thomas-maurice/SmartSensorWifi/Web/doge.jpeg

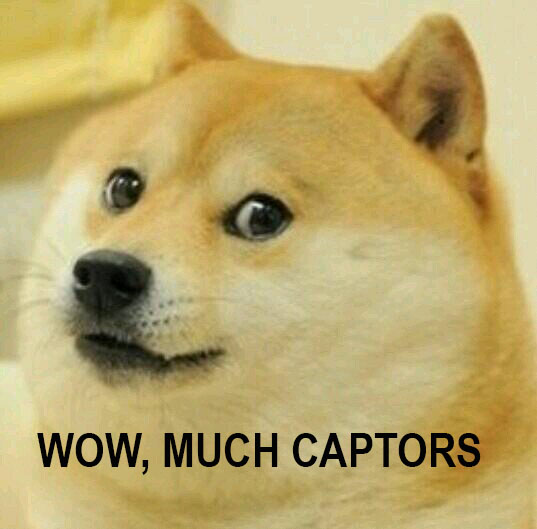
Web/doge.jpeg
