thomas-maurice/SmartSensorWifi/Arduino/src/ds1302.c

/*
 *
 *	Copyright (C) 2014 Thomas MAURICE <tmaurice59@gmail.com>
 *
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
 *	You should have received a copy of the GNU General Public License along
 *	with this program; if not, write to the Free Software Foundation, Inc.,
 *	51 Franklin Street, Fifth Floor, Boston, MA 02110-1301 USA.
 */

/**
 * \file ds1302.c
 * \author Thomas Maurice
 * 
 * \brief Implements an interface to the DS1302 RTC chip
 * \version 0.1
 * 
 */

#include <ds1302.h>

/**
 * Initializes the data transfert between the RTC and the chip.
 * This will configure the DDR as well as the initial state of
 * the lines.
 */
void ds1302_init_transfert() {
	// Set CE low and as an output
	sbi(DS1302_CE_DDR, DS1302_CE_PIN);
	cbi(DS1302_CE_PORT, DS1302_CE_PIN);
	
	// Set the clock low and as an output
	sbi(DS1302_CLK_DDR, DS1302_CLK_PIN);
	cbi(DS1302_CLK_PORT, DS1302_CLK_PIN);
	
	// Finally start the transfert setting the CE high
	sbi(DS1302_CE_PORT, DS1302_CE_PIN);
	
	_delay_us(4);
}

/**
 * Closes all the data transfers. This will disable the RTC CE line.
 */
void ds1302_end_transfert() {
	// Finally end the transfert setting the CE low
	cbi(DS1302_CE_PORT, DS1302_CE_PIN);
	
	_delay_us(4);
}

/**
 * Shifts a byte to the RTC
 * 
 * \param [in] byte The byte to shift
 */
void ds1302_shift_byte(uint8_t byte) {
	for(uint8_t i = 0; i < 8; i++) {
		cbi(DS1302_IO_PORT, DS1302_IO_PIN);
		DS1302_IO_PORT |= (((gbi(byte,i))<<DS1302_IO_PIN));
		_delay_us(1);
		sbi(DS1302_CLK_PORT, DS1302_CLK_PIN);
		_delay_us(1);
		cbi(DS1302_CLK_PORT, DS1302_CLK_PIN);
		_delay_us(1);
	}
}

/**
 * This function will write to a register of the RTC. This function
 * can be user either to configure the chip or to use the general
 * purpose ram.
 * 
 * \param [in] addr The address to write
 * \param [in] value The value to write
 * \param [in] target The target. Is either the clock register or the RAM register.
 * This value has either DS1302_CLOCK or DS1302_RAM value.
 */
void ds1302_write_register(uint8_t addr, uint8_t value, uint8_t target) {
	ds1302_init_transfert();
	uint8_t cmd = 0x0;
	cmd |= 0x80 | target | DS1302_WRITE_BYTE; // We want to write
	cmd |= ((addr&0x1F) << 1); // Let's put the address
	
	// Now we shift out the whole thing
	ds1302_shift_byte(cmd);
	ds1302_shift_byte(value);
	
	ds1302_end_transfert();
}

/**
 * Read the value stored in a register of the chip and returns it. This
 * function can be user either to read the chip or to use the general
 * purpose ram.
 * 
 * \param [in] addr The address to read
 * \param [in] target The target. Is either the clock register or the RAM register.
 * This value has either DS1302_CLOCK or DS1302_RAM value.
 * 
 * \return The value read
 */
uint8_t ds1302_read_register(uint8_t addr, uint8_t target) {
	ds1302_init_transfert();
	uint8_t cmd = 0x0;
	cmd |= 0x80 | target | DS1302_READ_BYTE; // We want to read from the clock
	cmd |= ((addr) << 1); // Let's put the address
	uint8_t res = 0x0;
	
	// Put the I/O line to output
	sbi(DS1302_IO_DDR, DS1302_IO_PIN);
	
	// Now we shift out the whole thing
	ds1302_shift_byte(cmd);
	
	// Put IO line to input & disable pull up
	cbi(DS1302_IO_DDR, DS1302_IO_PIN);
	cbi(DS1302_IO_PORT, DS1302_IO_PIN);
	
	for(uint8_t i = 0; i < 8; i++) {
		res |= (gbi(DS1302_IO_RD_PORT, DS1302_IO_PIN)<<i);
		
		_delay_us(1);
		sbi(DS1302_CLK_PORT, DS1302_CLK_PIN);
		_delay_us(1);
		cbi(DS1302_CLK_PORT, DS1302_CLK_PIN);
		_delay_us(1);
	}
	
	// Restore the I/O line to output
	sbi(DS1302_IO_DDR, DS1302_IO_PIN);
	cbi(DS1302_IO_PORT, DS1302_IO_PIN);
	
	ds1302_end_transfert();
	
	return res;
}

/**
 * Creates a timestring for the current date following the format :
 * DD/MM/YY HH:MM:SS so it is 18 chars long, including the null terminator.
 * 
 * \param [inout] time_string the pointer on the memory zone needed.
 */
void get_time_string(char* time_string) {
	uint8_t result = 0;
	result = ds1302_read_register(DS1302_SECONDS, DS1302_CLOCK);
	time_string[16] = (result & 0x0F) + '0';
	time_string[15] = ((result>>4) & 0x0F) + '0';
	time_string[14] = ':';
	result = ds1302_read_register(DS1302_MINUTES, DS1302_CLOCK);
	time_string[13] = (result & 0x0F) + '0';
	time_string[12] = ((result>>4) & 0x0F) + '0';
	time_string[11] = ':';
	result = ds1302_read_register(DS1302_HOURS, DS1302_CLOCK);
	time_string[10] = (result & 0x0F) + '0';
	time_string[9] = ((result>>4) & 0x0F) + '0';
	time_string[8] = ' ';
	result = ds1302_read_register(DS1302_YEAR, DS1302_CLOCK);
	time_string[7] = (result & 0x0F) + '0';
	time_string[6] = ((result>>4) & 0x0F) + '0';
	time_string[5] = '/';
	result = ds1302_read_register(DS1302_MONTH, DS1302_CLOCK);
	time_string[4] = (result & 0x0F) + '0';
	time_string[3] = ((result>>4) & 0x0F) + '0';
	time_string[2] = '/';
	result = ds1302_read_register(DS1302_DATE, DS1302_CLOCK);
	time_string[1] = (result & 0x0F) + '0';
	time_string[0] = ((result>>4) & 0x0F) + '0';
}

/**
 * Clears the CH bit. This will allow the clock to start.
 */
void ds1302_clear_clock_halt() {
	uint8_t r = ds1302_read_register(DS1302_SECONDS, DS1302_CLOCK);
	ds1302_write_register(DS1302_SECONDS, r & 0x7F, DS1302_CLOCK);
}

/**
 * Sets the time to the chip. The value are provided in natural binary,
 * the function will convert it to BCD.
 * 
 * \param [hrs] Hours
 * \param [mins] Minutes
 * \param [secs] Seconds
 */
void ds1302_set_time(uint8_t hrs, uint8_t mins, uint8_t secs) {
	ds1302_write_register(DS1302_SECONDS, dec_to_bcd(secs), DS1302_CLOCK);
	ds1302_write_register(DS1302_MINUTES, dec_to_bcd(mins), DS1302_CLOCK);
	ds1302_write_register(DS1302_HOURS, dec_to_bcd(hrs), DS1302_CLOCK);
}

/**
 * Sets the time to the chip. The value are provided in natural binary,
 * the function will convert it to BCD.
 * 
 * \param [day] Day
 * \param [month] Month
 * \param [year] Year
 */
void ds1302_set_date(uint8_t day, uint8_t month, uint16_t year) {
	ds1302_write_register(DS1302_DATE, dec_to_bcd(day), DS1302_CLOCK);
	ds1302_write_register(DS1302_MONTH, dec_to_bcd(month), DS1302_CLOCK);
	ds1302_write_register(DS1302_YEAR, dec_to_bcd(year%100), DS1302_CLOCK);
}

/**
 * Gets the time from the chip. This is in natural binary, no BCD.
 * 
 * \param [day] Day
 * \param [month] Month
 * \param [year] Year
 */
void ds1302_get_date(uint8_t* day, uint8_t* month, uint8_t* year) {
	*day = bcd_to_dec(ds1302_read_register(DS1302_DATE, DS1302_CLOCK));
	*month = bcd_to_dec(ds1302_read_register(DS1302_MONTH, DS1302_CLOCK));
	*year = bcd_to_dec(ds1302_read_register(DS1302_YEAR, DS1302_CLOCK));
}

/**
 * Gets the time from the chip. This is in natural binary, no BCD.
 * 
 * \param [hrs] Hours
 * \param [mins] Minutes
 * \param [secs] Seconds
 */
void ds1302_get_time(uint8_t* hrs, uint8_t* mins, uint8_t* secs) {
	*secs = bcd_to_dec(ds1302_read_register(DS1302_SECONDS, DS1302_CLOCK));
	*mins = bcd_to_dec(ds1302_read_register(DS1302_MINUTES, DS1302_CLOCK));
	*hrs = bcd_to_dec(ds1302_read_register(DS1302_HOURS, DS1302_CLOCK));
}

/**
 * Clears the WP bit, this will enables you to write to the chip.
 */
void ds1302_clear_write_protect() {
	ds1302_write_register(DS1302_WP, 0x0, DS1302_CLOCK);
}
