thomas-maurice/SmartSensorWifi/Arduino/src/timer.c

#include <timer.h>

void init_timer(void) {
	TCCR1B |= _BV(WGM12); // CTC mode with value in OCR1A 
	TCCR1B |= _BV(CS12);  // CS12 = 1; CS11 = 0; CS10 =1 => CLK/1024 prescaler
	TCCR1B |= _BV(CS10);
	OCR1A   = 255;
	TIMSK1 |= _BV(OCIE1A);
}
