thomas-maurice/SmartSensorWifi/Arduino/src/adc.c

/*
 *
 *	Copyright (C) 2014 Thomas MAURICE <tmaurice59@gmail.com>
 *
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
 *	You should have received a copy of the GNU General Public License along
 *	with this program; if not, write to the Free Software Foundation, Inc.,
 *	51 Franklin Street, Fifth Floor, Boston, MA 02110-1301 USA.
 */

/**
 * \file adc.c
 * \author Thomas Maurice
 * 
 * \brief ADC management file
 * \version 0.1
 * 
 */

#include <adc.h>

/**
 * Initializes the ADC.
 */
void adc_init() {
	ADMUX=(1<<REFS0)|(1<<ADLAR);
	ADCSRA=(1<<ADEN)|(1<<ADPS2)|(1<<ADPS1)|(1<<ADPS0);
}

/**
 * Gets a sample of the ADC on channel channel. The conversion will be
 * converted from 10 to 8 bits. So you'll lose the 2 LSB.
 * 
 * @todo Implement a 10 bit version, just in case.
 * 
 * @param [in] channel The channel you want to sample
 * 
 * @return The value of the channel
 */
uint8_t adc_get_sample(uint8_t channel) {
	ADMUX=(ADMUX&0xF0)|channel;
	ADCSRA|=(1<<ADSC);
	while((ADCSRA&(1<<ADSC))!=0);
	return ADCH; // High part of the conversion. 2 LSB omitted
}

/**
 * Converts an integer value from the ADC to a string and stores it into
 * the string str.
 * 
 * \param [in] channel the channel to convert
 * \param [out] str The final string. Must be of length 4, the \0 will be added by the function
 */
void adc_to_char(int channel, char* str) {
	int c = adc_get_sample(channel);
	str[0] = (c/100)+48;
	str[1] = (c/10)%10+48;
	str[2] = c%10+48;
	str[3] = '\0';
}

/**
 * Sends the conversion of the ADC channel channel to the serial port.
 * 
 * \param [in] channel The channel to get a dample from.
 */
void adc_print_conv(int channel) {
	char s[4];
	adc_to_char(channel, s);
	serial_send_string(s, strlen(s));
	serial_send_string("\r\n", 2);
}
